martijncasteel/launchpad/images/b-cu.png

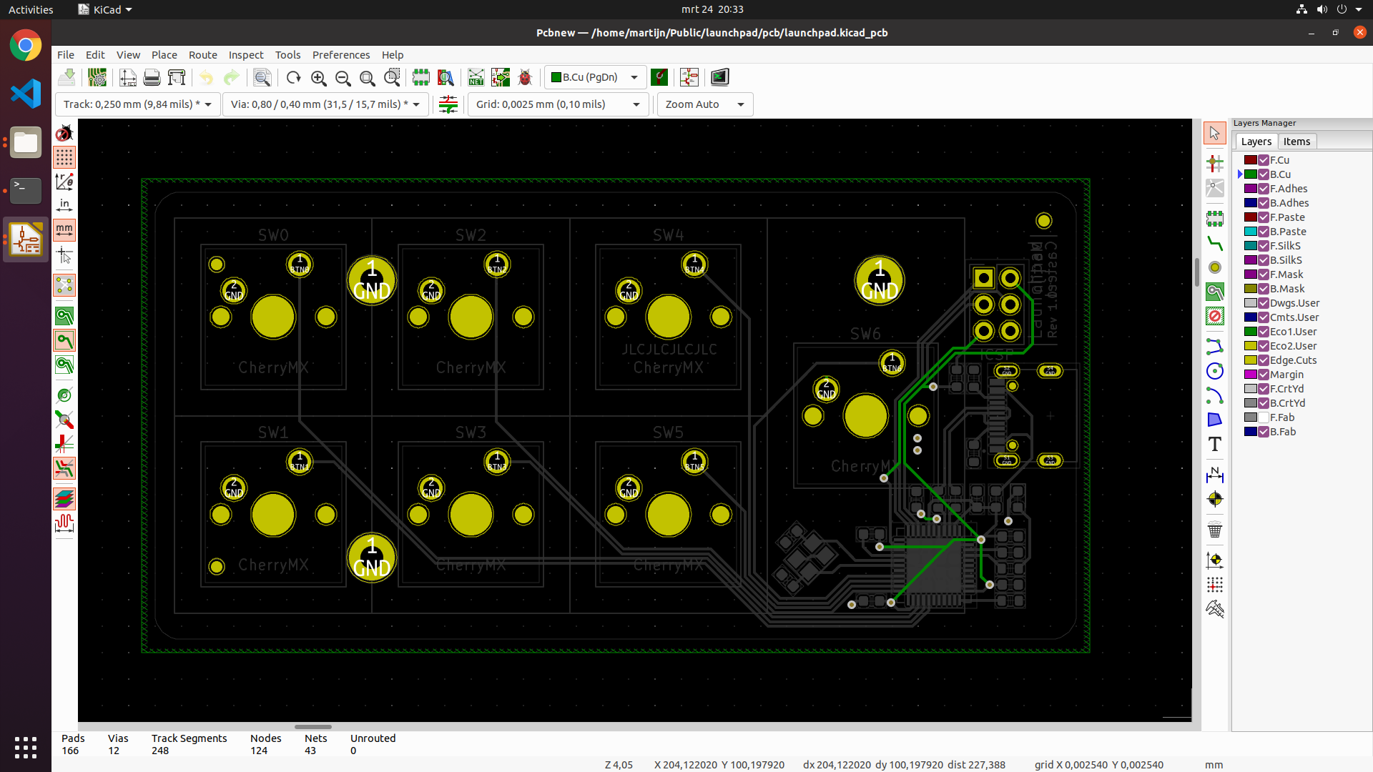
images/b-cu.png
