martijncasteel/launchpad/code/src/usb.c

/**
 * @file usb.c
 * @brief USB controller initialization, sending descriptors, and handle interrupts.
 * 
 * This contains all the logic for creating a usb hid device, the descriptors are 
 * placed in usb.h. At first the init command should be called to initialize the 
 * usb handshake, after that interrupts will be handeld to send data to the host.
 * 
 * @author Martijn Casteel
 * @date 2022-12-22
 */

#include "usb.h"

#include <stdlib.h>
#include <string.h>
#include <avr/io.h>
#include <avr/pgmspace.h>
#include <avr/interrupt.h>

uint8_t configuration = 0;
uint8_t clear_report = 0;
uint8_t idle_duration;

data_t *data; // struct with din and dout

/**
 * Initializes usb controller and sets interrupts to do further initialization.
 * This device is put in full-speed mode (pulling D+ high at the start) and is 
 * powered using the usb connection.
 * 
 * This function returns an address to be used for updating the usb reports.
 * 
 * @returns memory address for usb data
 */
data_t* usb_init() {
  cli();                                  // global interrrupt disabled

  USBCON &= ~(0x01 << USBE);              // reset USB controller
  USBCON |= (0x01 << USBE);

  USBCON &= ~(0x01 << FRZCLK);            // unfreeze the clock
  
  UHWCON |= (1 << UVREGE);                // enable USB pads regulator
  USBCON |= (0x01 << OTGPADE) |           // enable VBUS pads
    (0x01 << VBUSTE);                     // enable VBUS interrupt
  
  UDCON &= ~(1 << LSM);                   // use full speed mode
  UDCON &= ~(1 << DETACH);                // pull D+ high for attaching to host

  sei();                                  // global interrupt enabled

  data = (data_t *) malloc(sizeof(data_t)); // initialize register
  memset(data, 0, sizeof(data_t));
  return data;
}


/**
 * The general interrupts of the USB controller are covered here. As soon 
 * as the VBUS interrupt is triggered the PLL is configured. 
 * 
 * Sends the data buffer based on actual state of the pressed buttons.
 * Within USB the host starts all communication, the SOFI will request for
 * data. After sending data buffer is cleared.
 * 
 */
ISR(USB_GEN_vect){

  /**
   * VBUS interrupt is performed when connecting to the device
   */
  if (USBINT & (1 << VBUSTI)) {           // VBUS interrupt is active
    USBINT &= ~(1 << VBUSTI);             // clear interrupt flag

    if (USBSTA & (1 << VBUS)){            // check if device is connected
      PLLCSR |= (1 << PINDIV) |           // use 16 MHz oscillator
        (1 << PLLE);                      // enable PLL

      while (!(PLLCSR & (1 << PLOCK)))
        ; // wait until oscillator is stabilized

      UDIEN |= (1 << EORSTE) |            // end of reset interrupt enabled
        (1 << SOFE);                      // enable start of frame interrupt

      // device is powered!
      configuration = 0;
      
    } else {
      // device is unattached
      PLLCSR = 0x00;

    }

    return;
  }


  uint8_t udint = UDINT;                   // read UDINT register once
  UDINT = 0;
  
  /**
   * End of reset interupt
   */
  if (udint & (1 << EORSTI)) {
    UDINT &= ~(1 << EORSTI);              // reset interrupt flag

    UENUM = 0x00;                         // select endpoint 0
    UECONX = (1 << EPEN);                 // enable the endpoint
    UECFG0X &= ~(1 << EPDIR);             // OUT endpoint
    UECFG1X |= (1 << EPSIZE1) |           // 32 bytes endpoint
      (1 << ALLOC);                       // allocate it
    
    configuration = 0;      

    if (!(UESTA0X & (1 << CFGOK)))
      return;                             // UECFG1X should be reprogrammed
    
    UERST = 0x01;                         // reset endpoint
    UERST = 0x00;

    UEIENX = (1 << RXSTPE);               // enable receive setup packet interrupt
    return;
  }
  

  /**
   * Start of frame interrupt if usb is configured correctly and set configuration
   * is used to set the data endpoint.
   */
  if ((udint & (1 << SOFI)) && configuration ){ 
    UDINT &= ~(1 << SOFI);                // clear interrupt flag
    UENUM = 0x01;                         // endpoint for launchpad reports

    if (UEINTX & (1 << RWAL)) {           // check if banks are writeable
      send_dout_data(&(data->dout));      // create report

      UEINTX = (1 << RWAL) | (1 << NAKOUTI) | (1 << RXSTPI) | (1 << STALLEDI);
    }

    return;
  }
}


/**
 * USB communication request, used for setting up the handshake. Either a request
 * for (1) setting the address, (2) device descriptor, (3) string descriptors,
 * (4) configuration descriptor having a reference to an interface descriptor, 
 * a HID descriptor, or an endpoint descriptor.
 * 
 * After setting up the device and configuration, the interface (5) will be 
 * specified using the interface as recipient and using a report descriptor.
 * 
 */
ISR(USB_COM_vect) {
  UENUM = 0x00; // endpoint number is 0, 0 is the default configuration endpoint

  // USB endpoint interrupt and setup interrupt flag, setup interrupt flag is set
  // for every message the host initiates. Setup contains requesttype, request, 
  // value, index, and length.
  if (UEINTX & (1 << RXSTPI)) {  

    // UADATX reads data byte for byte, see table 9-2 of USB2.0 spec
    // decoding the setup package below.
    uint8_t bmRequestType = UEDATX;
    uint8_t bRequest = UEDATX;

    uint16_t wValue = UEDATX;
    wValue |= UEDATX << 8;
      
    uint16_t wIndex = UEDATX;
    wIndex |= UEDATX << 8;

    // wlenght is the expected length of the response for this request
    uint16_t wLength = UEDATX; 
    wLength |= UEDATX << 8;
  
    // Clear the interrupts, ensure to do this after reading UEDATX since they 
    // will be cleared. received setup interrupt flag, received out data interrupt 
    // flag, ready interrupt flag
    UEINTX &= ~((1 << RXSTPI) | (1 << RXOUTI) | (1 << TXINI)); 


    /* USB device requests*/

    if (bRequest == SET_ADDRESS && bmRequestType == DEVICE_IN) {

      UEINTX &= ~(1 << TXINI);
      while (!(UEINTX & (1 << TXINI)))
        ;  // Wait until the banks are ready

      UDADDR = wValue | (1 << ADDEN);  // Set the device address
      return;
    } 

    if (bRequest == GET_DESCRIPTOR && bmRequestType == DEVICE_OUT) {

      // get type and index from wValue
      uint8_t type = (wValue >> 8);
      uint8_t index = wValue; 

      // request device descriptor, only one present
      if(type == DEVICE) {
        send_pgm_data((uint8_t*)device_descriptor, pgm_read_byte(device_descriptor), wLength);
        return;

      } else if (type == QUALIFIER){
        // request error USB2.0 9.6.2, we only need full-speed
        UECONX |= (1 << STALLRQ) | (1 << EPEN);
        return;

      } else if (type == CONFIGURATION) {
        send_pgm_data((uint8_t*)configuration_descriptor, CONFIG_SIZE, wLength);
        return;

      } else if (type == STRING) {

        if (index == 0) {         // return supported language codes

          uint16_t langids[] = {
            0x0409,               // English (United States)
            0x0413                // Dutch (Netherlands)
          };

          send_uint16_data(langids, sizeof(langids), wLength);
          return;

        }else if (index == 1){    // iManufacturer string descriptor

          //004d 0061 0072 0074 0069 006a 006e 0020 0043 0061 0073 0074 0065 0065 006c
          uint16_t manufactorer[] = MANUFACTORER;

          send_uint16_data(manufactorer, sizeof(manufactorer) - 2, wLength);
          return;

        } else if (index == 2){   // iProduct string descriptor

          // 004c 0061 0075 006e 0063 0068 0070 0061 0064
          uint16_t name[] = PRODUCTNAME;

          send_uint16_data(name, sizeof(name) - 2, wLength);
          return;
      
        }
      }

      // host made an invalid request, stall
      UECONX |= (1 << STALLRQ) | (1 << EPEN);
      return;
    }

    if (bRequest == SET_CONFIGURATION && bmRequestType == DEVICE_IN) {
      configuration = wValue & 255;

      UEINTX &= ~(1 << TXINI);

      UENUM = 0x01;
      UECONX = (1 << EPEN);

      UECFG0X |= (1 << EPDIR) |           // IN endpoint
        (1 << EPTYPE1) | (1 << EPTYPE0);  // interrupt endpoint
      UECFG1X |= (1 << EPBK0) |           // double bank
        (1 << ALLOC);                     // allocate 8 bytes

      UERST = 0x1E;                       // reset all endpoints
      UERST = 0;

      return;
    }

    if (bRequest == GET_CONFIGURATION && bmRequestType == DEVICE_OUT) {
      // Wait for banks to be ready for data transmission
      while (!(UEINTX & (1 << TXINI)))
        ;  

      UEDATX = configuration;             // send current configuration value
      UEINTX &= ~(1 << TXINI);

      return;
    }

    if (bRequest == GET_STATUS && bmRequestType == DEVICE_OUT) {
      while (!(UEINTX & (1 << TXINI)))
        ;
      UEDATX = 0;
      UEDATX = 0;
      UEINTX &= ~(1 << TXINI);
      return;
    }
  
    /* HID class specific requests */

    if (bRequest == GET_DESCRIPTOR && bmRequestType == (INTERFACE_OUT)) {
      // get type from wValue
      uint8_t type = (wValue >> 8);

      if (type == HID_DESCRIPTOR) {
        // offset used to retrieve the hid descriptor part from the config descriptor
        const uint8_t* hid_descriptor = configuration_descriptor + 18;
        send_pgm_data((uint8_t*)hid_descriptor, pgm_read_byte(hid_descriptor), wLength);
        return;

      } else if (type == REPORT) {
        send_pgm_data((uint8_t*)report_descriptor, REPORT_SIZE, wLength);
        return;
      }
    
    }

    if (bRequest == SET_REPORT && bmRequestType == (INTERFACE_IN | CLASS)) {
      while (!(UEINTX & (1 << RXOUTI)))
        ; // wait for banks ready to read

        uint8_t _ = UEDATX;               // ignore report id
        data->din = UEDATX;               // read bits for LED

        // eunum maybe?

        UEINTX &= ~(1 << TXINI);
        // UEINTX &= ~(1 << RXOUTI);         // TODO check this, looks like no response, maybe wrong endpoint?
        return;
    }

    if (bRequest == GET_REPORT && bmRequestType == (INTERFACE_OUT | CLASS)) {
      
      while (!(UEINTX & (1 << TXINI)))
        ; // Wait for banks to be ready for data transmission

      send_dout_data(&(data->dout));      // create report

      UEINTX &= ~(1 << TXINI);
      return;
    }

    if (bRequest == SET_IDLE && bmRequestType == (INTERFACE_IN | CLASS)) { 
      idle_duration = wValue & 255;       // get idle duration

      UEINTX &= ~(1 << TXINI);            // Send ACK and clear TX bit
      return;
    }

    if (bRequest == GET_IDLE && bmRequestType == (INTERFACE_OUT | CLASS)) { 
      // Wait for banks to be ready for data transmission
      while (!(UEINTX & (1 << TXINI)))
        ;

      UEDATX = idle_duration;

      UEINTX &= ~(1 << TXINI);
      return;
    }
  }

  UECONX |= (1 << STALLRQ) | (1 << EPEN); // invalid request
}


/**
 * Sends descriptors stored in PROGMEM (program memory)
 * 
 * @param descriptor pointer to PROGMEM data
 * @param length number of bytes
 * @param wLength requested length from host
 */
int8_t send_pgm_data(uint8_t* descriptor, uint8_t length, uint16_t wLength) {
  uint8_t* data = descriptor;
  uint16_t lbyte = length > wLength ? wLength : length; // only send what is asked for

  while (lbyte > 0) {

    // Wait for banks to be ready for data transmission
    while (!(UEINTX & (1 << TXINI)))
      ;
    
    if (UEINTX & (1 << RXOUTI))
      return -1;  // If there is another packet, exit to handle it

    // split it up in packages
    uint8_t packet = lbyte > PACKETSIZE ? PACKETSIZE: lbyte; 

    for (int i = 0; i < packet; i++) {
      // data is stored in flash so read using pgm_read_byte
      UEDATX = pgm_read_byte(data + i);
    }

    lbyte -= packet;
    data += packet; // move pointer
    UEINTX &= ~(1 << TXINI);
  }

  return 0;
}


/**
 * Send string data in *one* packet with the string descriptor request.
 * @note Current implementation allows reports up to PACKETSIZE bytes.
 * 
 * @param data pointer to actual data 
 * @param length number of bytes
 * @param wLength requested length from host
*/
int8_t send_uint16_data(uint16_t* data, uint8_t length, uint16_t wLength) {
  uint16_t* d = data;
  uint16_t lbyte = (length + 2) > wLength ? wLength : (length + 2); // TODO optimize?
  uint16_t lchar = (lbyte - 2) / 2; // number of uint16 in data, at most wLength

  // Wait for banks to be ready for data transmission
  while (!(UEINTX & (1 << TXINI)))
    ;

  if (UEINTX & (1 << RXOUTI))
    return -1;  // If there is another packet, exit to handle it

  UEDATX = length + 2;
  UEDATX = 0x03; // string descriptor

  for (int i = 0; i < lchar; i++) {
    uint16_t character = *(d + i); // two byte unicode

    UEDATX = (character & 255);
    UEDATX = (character >> 8) & 255;
  }

  UEINTX &= ~(1 << TXINI);
  return 0;
}

/**
 * Small function to send the dout register to UEDATX, a byte at a time. 
 * The register consists of multiple reports, every byte holds a report, 
 * see the report descriptor for more information. 
 * 
 * If the second byte has data, the second byte will be cleared and the 
 * data will be send with report id 2. Afterwards an empty report should be
 * send to clear key presses. Otherwise only the first byte will
 * be cleared and send with report id 1. report 1 is then also the default.
 * 
 * @param dout pointer to data register
 */
int8_t send_dout_data(uint16_t* dout) {
  uint16_t data = *dout;

  if ((data & 255) > 0) {                 // second byte has data
    *dout = (data & 0xFF00);              // clear second byte in buffer

    UEDATX = 0x02;
    UEDATX = (data & 255);

    clear_report = 1;                     // send an empty message afterwards
    return 0;

  } else if (clear_report) {              // note their is probably a neater way
    UEDATX = 0x02;
    UEDATX = 0x00;                        // clear report to stop key being 'pressed down'

    clear_report = 0;
    return 0;

  } else {                                // send first byte as report 1
    *dout = (data & 255);                 // clear first byte
    UEDATX = 0x01;                        // report id
    UEDATX = (data >> 8) & 255;           // send report to buffer
    return 0;
  }
}
